kenblu24/gmu_ballonet/testing_pcb/ballonet/ballonet_esp32_proto.sch

## KiCad design testing_pcb/ballonet/ballonet_esp32_proto.sch (2021-04-29, an earlier design)

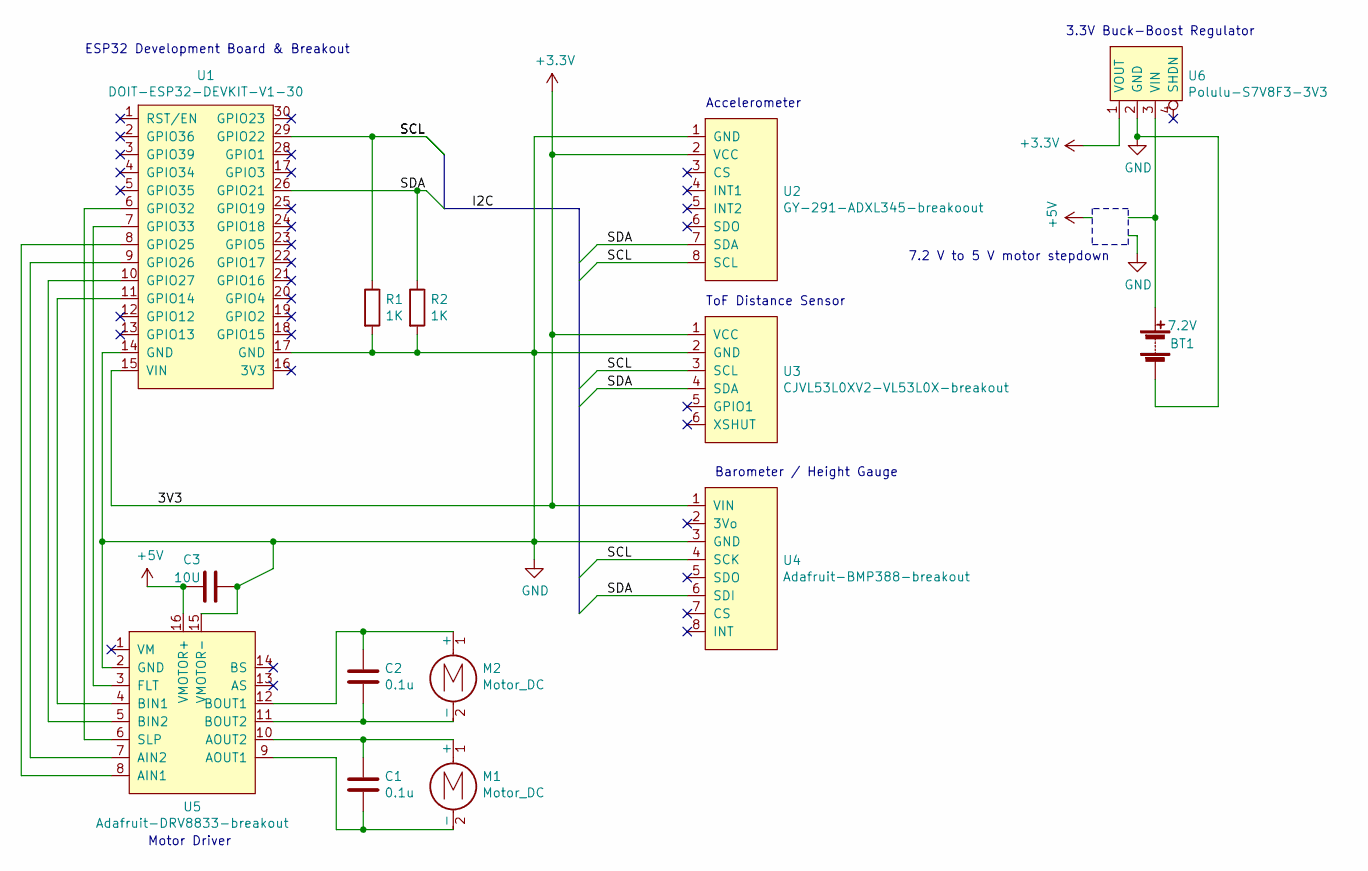
[picture p15: schematic ballonet_esp32_proto.sch]

Parts:
BT1: 7.2V
C1, C2: 0.1u
C3: 10U
M1, M2: Motor_DC
R1, R2: 1K
U1: DOIT-ESP32-DEVKIT-V1-30
U2: GY-291-ADXL345-breakoout
U3: CJVL53L0XV2-VL53L0X-breakout
U4: Adafruit-BMP388-breakout
U5: Adafruit-DRV8833-breakout
U6: Polulu-S7V8F3-3V3

Connections:
+3.3V: U1.15 (VIN), U2.2 (VCC), U3.1 (VCC), U4.1 (VIN), U6.1 (VOUT)
+5V: C3.2, U5.16 (VMOTOR+)
GND: BT1.2 (-), C3.1, R1.2, R2.2, U1.14 (GND), U1.17 (GND), U2.1 (GND), U3.2 (GND), U4.3 (GND), U5.2 (GND), U5.15 (VMOTOR-), U6.2 (GND)
unnamed: BT1.1 (+), U6.3 (VIN)
unnamed: C1.1, M1.1 (+), U5.10 (AOUT2)
unnamed: C1.2, M1.2 (-), U5.9 (AOUT1)
unnamed: C2.1, M2.1 (+), U5.12 (BOUT1)
unnamed: C2.2, M2.2 (-), U5.11 (BOUT2)
unnamed: U1.6 (GPIO32), U5.6 (SLP)
unnamed: U1.7 (GPIO33), U5.3 (FLT)
unnamed: U1.8 (GPIO25), U5.8 (AIN1)
unnamed: U1.9 (GPIO26), U5.7 (AIN2)
unnamed: U1.10 (GPIO27), U5.5 (BIN2)
unnamed: U1.11 (GPIO14), U5.4 (BIN1)
SCL: R1.1, U1.29 (GPIO22), U2.8 (SCL), U3.3 (SCL), U4.4 (SCK)
SDA: R2.1, U1.26 (GPIO21), U2.7 (SDA), U3.4 (SDA), U4.6 (SDI)

Notes on the sheet:
7.2 V to 5 V motor stepdown
3.3V Buck-Boost Regulator
Accelerometer
ToF Distance Sensor
Barometer / Height Gauge
Motor Driver
ESP32 Development Board & Breakout
