kenblu24/gmu_ballonet/micropython_root/adxl345.py

'''ADXL345 Python library for Raspberry Pi
#
# author:  Jonathan Williamson
# license: BSD, see LICENSE.txt included in this package
#
# This is a Raspberry Pi Python implementation to help you get started with
# the Adafruit Triple Axis ADXL345 breakout board:

# This file has been modified to work with the ESP32 running Micropython
# -- Kevin Zhu
'''

# ADXL345 constants
EARTH_GRAVITY_MS2 = 9.80665
SCALE_MULTIPLIER = 0.004

DATA_FORMAT = 0x31
BW_RATE = 0x2C
POWER_CTL = 0x2D

BW_RATE_1600HZ = 0x0F
BW_RATE_800HZ = 0x0E
BW_RATE_400HZ = 0x0D
BW_RATE_200HZ = 0x0C
BW_RATE_100HZ = 0x0B
BW_RATE_50HZ = 0x0A
BW_RATE_25HZ = 0x09

RANGE_2G = 0x00
RANGE_4G = 0x01
RANGE_8G = 0x02
RANGE_16G = 0x03

MEASURE = 0x08
AXES_DATA = 0x32

class ADXL345:

    address = None

    def __init__(self, i2c, address=83):
        self.i2c = i2c
        self.address = address
        self.setBandwidthRate(BW_RATE_100HZ)
        self.setRange(RANGE_2G)
        self.enableMeasurement()

    def enableMeasurement(self):
        self.i2c.writeto_mem(self.address, POWER_CTL, MEASURE.to_bytes(1, 'big'))

    def setBandwidthRate(self, rate_flag):
        self.i2c.writeto_mem(self.address, BW_RATE, rate_flag.to_bytes(1, 'big'))

    # set the measurement range for 10-bit readings
    def setRange(self, range_flag):
        value = self.i2c.readfrom_mem(self.address, DATA_FORMAT, 1)
        value = int.from_bytes(value, 'big')

        value &= ~0x0F
        value |= range_flag
        value |= 0x08

        self.i2c.writeto_mem(self.address, DATA_FORMAT, value.to_bytes(1, 'big'))

    # returns the current reading from the sensor for each axis
    #
    # parameter gforce:
    #    False (default): result is returned in m/s^2
    #    True           : result is returned in gs
    def getAxes(self, gforce=False):
        bytes = self.i2c.readfrom_mem(self.address, AXES_DATA, 6)

        x = bytes[0] | (bytes[1] << 8)
        if(x & (1 << 16 - 1)):
            x = x - (1 << 16)

        y = bytes[2] | (bytes[3] << 8)
        if(y & (1 << 16 - 1)):
            y = y - (1 << 16)

        z = bytes[4] | (bytes[5] << 8)
        if(z & (1 << 16 - 1)):
            z = z - (1 << 16)

        # x = x * SCALE_MULTIPLIER
        # y = y * SCALE_MULTIPLIER
        # z = z * SCALE_MULTIPLIER

        if gforce is False:
            x = x * EARTH_GRAVITY_MS2
            y = y * EARTH_GRAVITY_MS2
            z = z * EARTH_GRAVITY_MS2

        x = round(x, 4)
        y = round(y, 4)
        z = round(z, 4)

        return {"x": x, "y": y, "z": z}


if __name__ == "__main__":
    # if run directly we'll just create an instance of the class and output
    # the current readings
    adxl345 = ADXL345()

    axes = adxl345.getAxes(True)
    print("ADXL345 on address 0x{}:".format(adxl345.address))
    print('   x = {:.3f}G'.format(axes['x']))
    print('   y = {:.3f}G'.format(axes['y']))
    print('   z = {:.3f}G'.format(axes['z']))
